jboone/robotron-fpga-verilog/rtl/rom_decoder_6.v

/* Copyright 2019 Jared Boone <jared@sharebrained.com>. Open-source license to be determined.
 */

`default_nettype none
`timescale 1ns / 100ps

module rom_decoder_6(
	input  wire        clock_i,
	input  wire        clock_enable_i,
	input  wire [ 8:0] address_i,
	output reg  [ 7:0] data_o
);

reg [7:0] mem[0:511];

initial
	$readmemh("build/decoder_6.hex", mem);

always @(posedge clock_i) begin
	if(clock_enable_i)
		data_o <= mem[address_i];
end

endmodule
